nickcoutsos/dactyl-deskmount/outputs/dactyl-deskmount.png

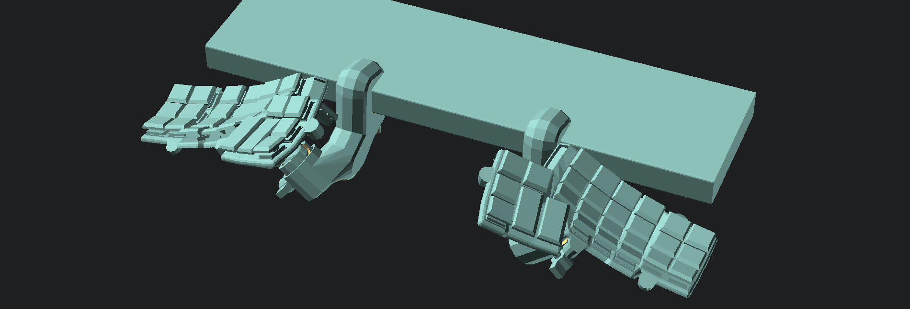
outputs/dactyl-deskmount.png
