nickcoutsos/dactyl-deskmount/outputs/finished-product/pro-micro-closeup.jpg

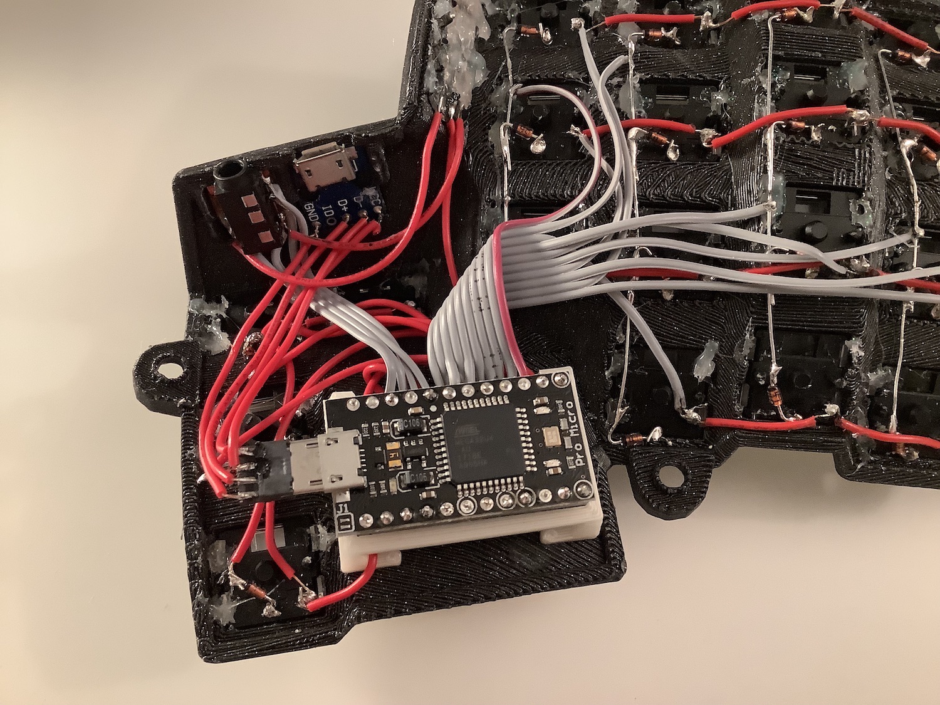
outputs/finished-product/pro-micro-closeup.jpg
