nickcoutsos/dactyl-deskmount/outputs/placeholders.png

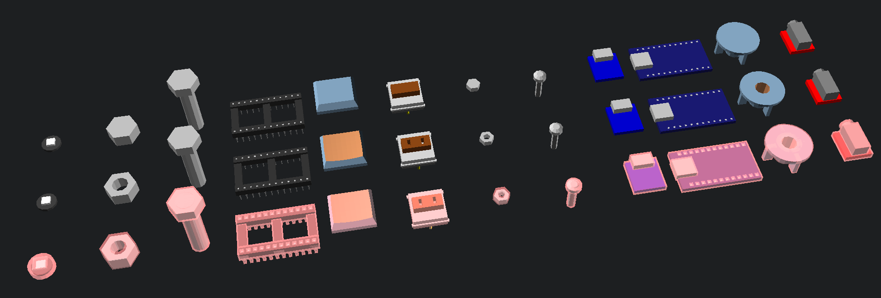
outputs/placeholders.png
