nickcoutsos/dactyl-deskmount/mount.scad

use <scad-utils/linalg.scad>
use <scad-utils/transformations.scad>

use <placeholders.scad>
use <positioning.scad>
use <util.scad>
use <main.scad>
use <table-hook.scad>
include <definitions.scad>

$fn = 12;
keyboard_offset = rotation([0, -20, 0]) * translation([30, 5, -6]);

module screw_and_nut_cutout() {
  translate([0, 0, 5]) cylinder(d=6.5, h=3);
  translate([0, 0, -1]) cylinder(d=3, h=6);
  scale([1, 1, 2]) translate([0, 0, -2]) m3_hex_nut($clearance=1);
  m3_hex_nut($clearance=.75);
}

mount_base_height = 8.5;

module mount() {
  difference() {
    union() {
      color("forestgreen") rotate([0, 0, -70]) cylinder(d=28, h=mount_base_height, $fn=24);

      color("mediumseagreen")
      multmatrix(keyboard_offset)
      difference() {
        serial_hulls() {
          post_place(0) translate([0, 0, -7 + .01]) cylinder(d=11, h=6);
          post_place(0) translate([0, 0, -7 + .01]) cylinder(d=6, h=5);
          post_place(0) translate([0, 6.5, -7 + .01]) cylinder(d=6, h=5);

          multmatrix(invert_rt(keyboard_offset))
          rotate([0, 0, 190])
            arc(r1=14, r2=12, h=mount_base_height, a=70);
        }

        post_place(0) translate([0, 0, -7]) screw_and_nut_cutout();
      }

      color("mediumseagreen")
      multmatrix(keyboard_offset)
      difference() {
        serial_hulls() {
          post_place(1) translate([0, 0, -7 + .01]) cylinder(d=11, h=6);
          post_place(1) translate([0, 0, -7 + .01]) cylinder(d=6, h=5);
          multmatrix(finger_place_transformation(1.2, 4)) translate([0, 0, -10]) sphere(r=3);
          multmatrix(finger_place_transformation(1.2, 3.5)) translate([0, 0, -10]) sphere(r=3.5);
          multmatrix(finger_place_transformation(1.2, 3)) translate([0, 0, -10]) sphere(r=3.5);
          multmatrix(finger_place_transformation(1.2, 2.5)) translate([0, 0, -10]) sphere(r=3.5);
          multmatrix(finger_place_transformation(1.2, 2)) translate([0, 0, -10]) sphere(r=3);
          multmatrix(finger_place_transformation(1.2, 1.5)) translate([0, 0, -10]) sphere(r=3);
          multmatrix(finger_place_transformation(1.2, 1)) translate([0, 0, -10]) sphere(r=3);
          post_place(2) translate([0, 0, -7 + .01]) cylinder(d=6, h=5);
          post_place(2) translate([0, 0, -7 + .01]) cylinder(d=11, h=6);
        }

        post_place(1) translate([0, 0, -7]) screw_and_nut_cutout();
        post_place(2) translate([0, 0, -7]) screw_and_nut_cutout();
      }

      color("mediumseagreen")
      multmatrix(keyboard_offset)
      hull() {
        multmatrix(finger_place_transformation(1.2, 3)) translate([0, 0, -10]) sphere(r=3.5);
        multmatrix(finger_place_transformation(1.2, 1.5)) translate([0, 0, -10]) sphere(r=3);
        multmatrix(invert_rt(keyboard_offset))
        rotate([0, 0, -70])
          arc(r1=14, r2=12, h=mount_base_height, a=140, $fn=24);
      }
    }

    tee_nut($clearance=1, footprint=true);
  }
}

// translate(desk_top_offset) table();
// mirror_axes([[1, 0, 0]]) translate([80, 0, 0])
ball_mount() {
  color("goldenrod") tee_nut();
  mount();

  translate(-[0, 0, 15.05+8.47])
  multmatrix($inverse_pivot_transform)
  table_hook([-26, 0, 0], $render_accessories=true);

  multmatrix(keyboard_offset) {
    assembled_plate($detail=false);
    accessories(
      $render_controller=true,
      $render_leds=true,
      $render_switches=true,
      $render_keycaps=true,
      $render_trrs=true,
      $key_pressed=false
    );

    for (i=[0:2]) post_place(i) {
      m3_screw();
      translate([0, 0, -7]) m3_hex_nut();
    }
  }
}

/// samples for test prints
// intersection() {
//   difference() {
//     mount();
//     tee_nut($clearance=1, footprint=true);
//     multmatrix(keyboard_offset) assembled_plate();
//   }

//   // ball mount socket
//   // table_hook([-26, 0, 0]);
//   // rotate(90, Z)
//   // rotate(60, X)
//   // rotate(180, Z)
//   // translate([0, 0, -25])
//   //   cylinder(d=40, h=10, center=true);

//   // nut holder
//   // #translate([10, -42, 22]) cylinder(d=12, h=12, center=true);
//   // base
//   // #translate([0, 0, -1]) cylinder(d=30, h=15);
// }
