nickcoutsos/dactyl-deskmount/placeholders.scad

include <definitions.scad>
